Am0k-GIT/Soldering_station/case/gx16-8.SLDPRT

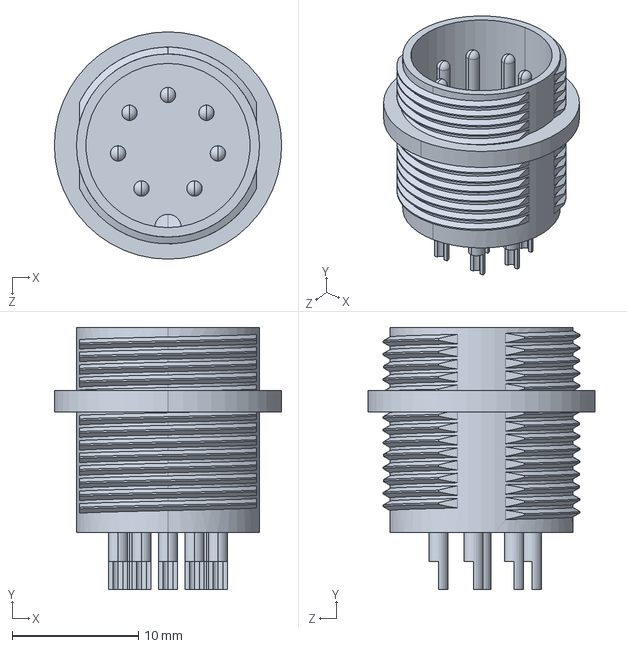
[picture p35: CAD file, 2025-12-07]
case/gx16-8.SLDPRT
18.0 x 20.8 x 18.0 mm
