Am0k-GIT/Soldering_station/case/shim_8_3.2_1.4.SLDPRT

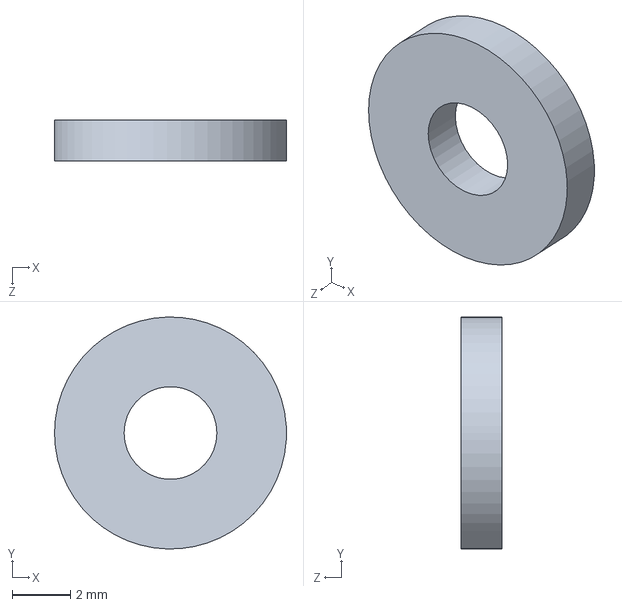
[picture p36: CAD file, 2025-12-07]
case/shim_8_3.2_1.4.SLDPRT
8.00 x 8.00 x 1.40 mm
