Am0k-GIT/Soldering_station/case/PC cooling fan.STEP

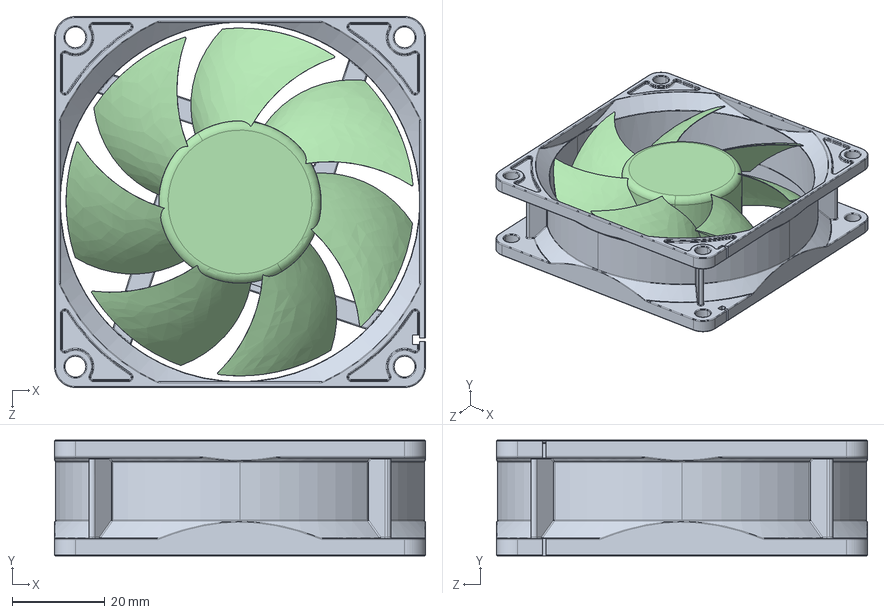
[picture p37: CAD file, 2025-12-07]
case/PC cooling fan.STEP
80.0 x 25.0 x 80.0 mm
fan body case
Part3^Assem1
fanl blade
