Am0k-GIT/Soldering_station/case/GX12-5 Jack.step

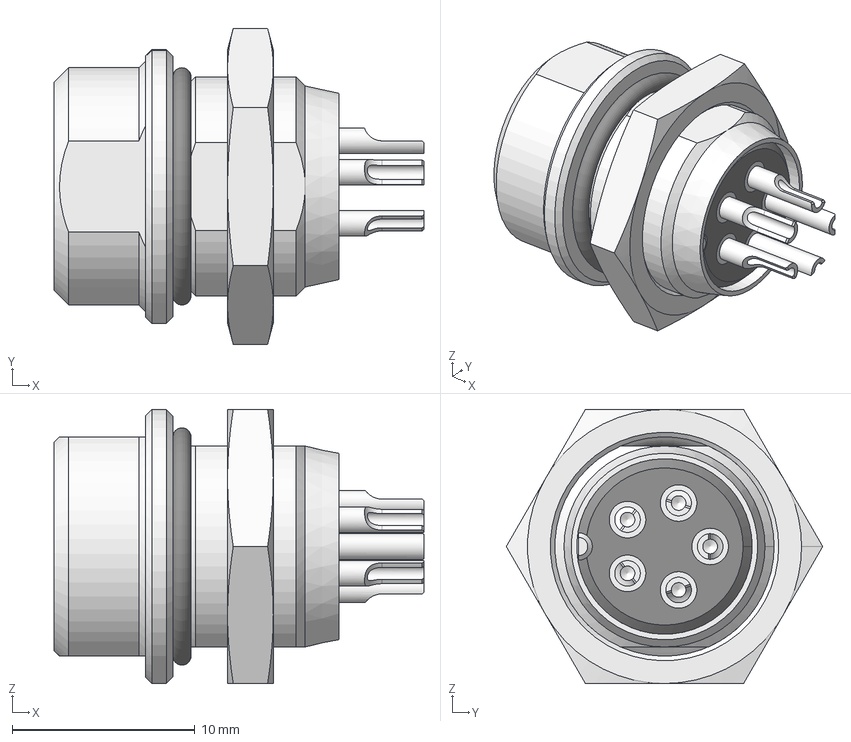
[picture p38: CAD file, 2025-12-07]
case/GX12-5 Jack.step
20.2 x 17.3 x 15.0 mm
