Am0k-GIT/Soldering_station/case/part_2.SLDPRT

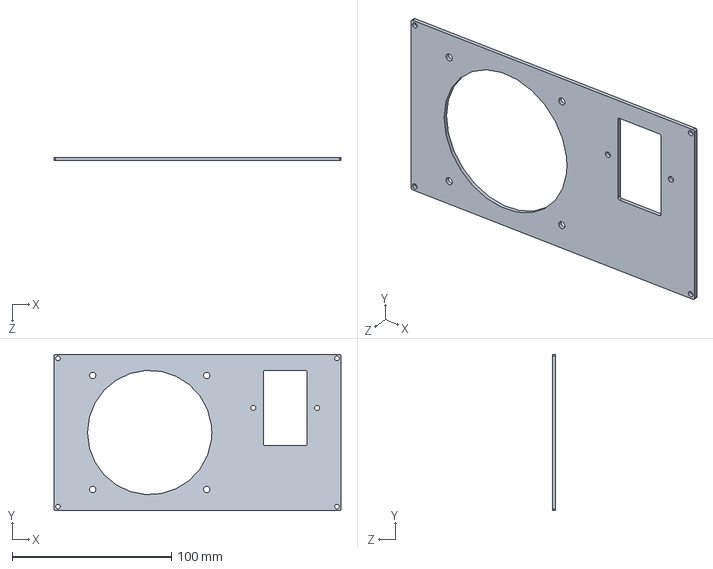
[picture p39: CAD file, 2025-12-07]
case/part_2.SLDPRT
180.0 x 98.0 x 2.00 mm
