Am0k-GIT/Soldering_station/case/frame.SLDPRT

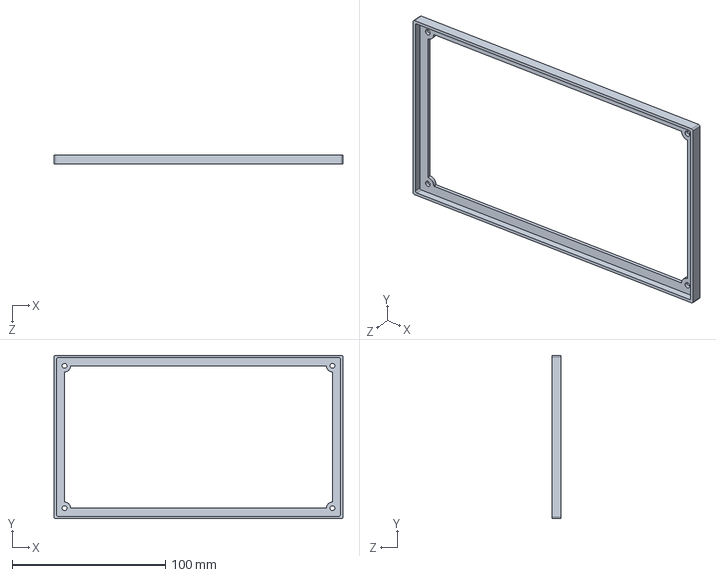
[picture p40: CAD file, 2025-12-07]
case/frame.SLDPRT
188.8 x 106.8 x 6.00 mm
