Am0k-GIT/Soldering_station/case/power_supply_mount.SLDPRT

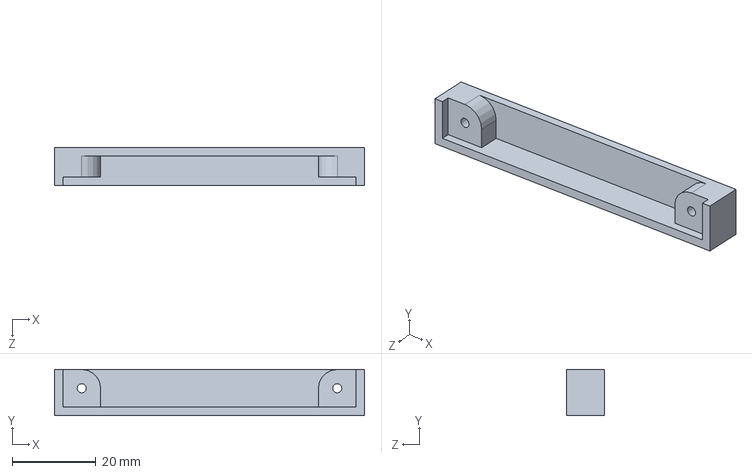
[picture p41: CAD file, 2025-12-07]
case/power_supply_mount.SLDPRT
74.0 x 11.0 x 9.00 mm
