Am0k-GIT/Soldering_station/software/Soldering_Station_260412/Core/Inc/24CXX/ee24.c

/************************************************************************************************************
**************    Include Headers
************************************************************************************************************/
#include "usart.h"

#include "ee24.h"
#if EE24_RTOS == EE24_RTOS_DISABLE
#elif EE24_RTOS == EE24_RTOS_CMSIS_V1
#include "cmsis_os.h"
#include "freertos.h"
#elif EE24_RTOS == EE24_RTOS_CMSIS_V2
#include "cmsis_os2.h"
#include "freertos.h"
#elif EE24_RTOS == EE24_RTOS_THREADX
#include "app_threadx.h"
#endif

/************************************************************************************************************
**************    Private Definitions
************************************************************************************************************/

#if (EE24_SIZE <= 2)
#define EE24_PSIZE     8
#elif (EE24_SIZE <= 16)
#define EE24_PSIZE     16
#else
#define EE24_PSIZE     32
#endif

/************************************************************************************************************
**************    Private Functions
************************************************************************************************************/

void EE24_Delay(uint32_t Delay);
void EE24_Lock(EE24_HandleTypeDef *Handle);
void EE24_UnLock(EE24_HandleTypeDef *Handle);

/***********************************************************************************************************/

void EE24_Delay(uint32_t Delay)
{
#if EE24_RTOS == EE24_RTOS_DISABLE
  HAL_Delay(Delay);
#elif (EE24_RTOS == EE24_RTOS_CMSIS_V1) || (EE24_RTOS == EE24_RTOS_CMSIS_V2)
  uint32_t d = (configTICK_RATE_HZ * Delay) / 1000;
  if (d == 0)
      d = 1;
  osDelay(d);
#elif EE24_RTOS == EE24_RTOS_THREADX
  uint32_t d = (TX_TIMER_TICKS_PER_SECOND * Delay) / 1000;
  if (d == 0)
    d = 1;
  tx_thread_sleep(d);
#endif
}

/***********************************************************************************************************/

void EE24_Lock(EE24_HandleTypeDef *Handle)
{
  while (Handle->Lock)
  {
    EE24_Delay(1);
  }
  Handle->Lock = 1;
}

/***********************************************************************************************************/

void EE24_UnLock(EE24_HandleTypeDef *Handle)
{
  Handle->Lock = 0;
}

/************************************************************************************************************
**************    Public Functions
************************************************************************************************************/

#if EE24_USE_WP_PIN == false
/**
  * @brief  Initialize EEPROM handle
  * @note   Initialize EEPROM handle and set EEPROM address
  *
  * @param  *Handle: Pointer to EE24_HandleTypeDef structure
  * @param  *HI2c: Pointer to I2C_HandleTypeDef structure
  * @param  I2CAddress: I2C Memory address
  *
  * @retval bool: true or false
  */
bool EE24_Init(EE24_HandleTypeDef *Handle, I2C_HandleTypeDef *HI2c, uint8_t I2CAddress)
{
  bool answer = false;
  do
  {
    if ((Handle == NULL) || (HI2c == NULL))
    {
      break;
    }
    Handle->HI2c = HI2c;
    Handle->Address = I2CAddress;
    if (HAL_I2C_IsDeviceReady(Handle->HI2c, Handle->Address, 2, 100) == HAL_OK)
    {
      answer = true;
    }
  }
  while (0);

  return answer;
}
#else
/**
  * @brief  Initialize EEPROM handle
  * @note   Initialize EEPROM handle and set memory address
  *
  * @param  *Handle: Pointer to EE24_HandleTypeDef structure
  * @param  *HI2c: Pointer to I2C_HandleTypeDef structure
  * @param  I2CAddress: I2C Memory address
  * @param  *GPIO_TypeDef: Pointer to GPIO_TypeDef structure for Write protected pin
  * @param  WpPin: PinNumber of write protected pin
  *
  * @retval bool: true or false
  */
bool EE24_Init(EE24_HandleTypeDef *Handle, I2C_HandleTypeDef *HI2c, uint8_t I2CAddress, GPIO_TypeDef *WpGpio, uint16_t WpPin)
{
  bool answer = false;
  do
  {
    if ((Handle == NULL) || (HI2c == NULL) || (WpGpio == NULL))
    {
      break;
    }
    Handle->HI2c = HI2c;
    Handle->Address = I2CAddress;
    Handle->WpGpio = WpGpio;
    Handle->WpPin = WpPin;
    HAL_GPIO_WritePin(Handle->WpGpio, Handle->WpPin, GPIO_PIN_SET);
    if (HAL_I2C_IsDeviceReady(Handle->HI2c, Handle->Address, 2, 100) == HAL_OK)
    {
      answer = true;
    }
  }
  while (0);

  return answer;
}
#endif

/***********************************************************************************************************/

/**
  * @brief  Read from Memory
  * @note   Read data from memory and copy to an array
  *
  * @param  *Handle: Pointer to EE24_HandleTypeDef structure
  * @param  Address: Start address for read
  * @param  *Data: Pointer to copy data from EEPROM
  * @param  Len: Data length to read
  * @param  Timeout: Timeout of this operation in ms
  *
  * @retval bool: true or false
  */
bool EE24_Read(EE24_HandleTypeDef *Handle, uint32_t Address, uint8_t *Data, size_t Len, uint32_t Timeout)
{
  EE24_Lock(Handle);
  bool answer = false;
  do
  {
#if ((EE24_SIZE == EE24_1KBIT) || (EE24_SIZE == EE24_2KBIT))
    if (HAL_I2C_Mem_Read(Handle->HI2c, Handle->Address, Address, I2C_MEMADD_SIZE_8BIT, Data, Len, Timeout) == HAL_OK)
#elif (EE24_SIZE == EE24_4KBIT)
    if (HAL_I2C_Mem_Read(Handle->HI2c, Handle->Address | ((Address & 0x0100) >> 7), (Address & 0xff), I2C_MEMADD_SIZE_8BIT, Data, Len, Timeout) == HAL_OK)
#elif (EE24_SIZE == EE24_8KBIT)
    if (HAL_I2C_Mem_Read(Handle->HI2c, Handle->Address | ((Address & 0x0300) >> 7), (Address & 0xff), I2C_MEMADD_SIZE_8BIT, Data, Len, Timeout) == HAL_OK)
#elif (EE24_SIZE == EE24_16KBIT)
    if (HAL_I2C_Mem_Read(Handle->HI2c, Handle->Address | ((Address & 0x0700) >> 7), (Address & 0xff), I2C_MEMADD_SIZE_8BIT, Data, Len, Timeout) == HAL_OK)
#else
    if (HAL_I2C_Mem_Read(Handle->HI2c, Handle->Address, Address, I2C_MEMADD_SIZE_16BIT, Data, Len, Timeout) == HAL_OK)
#endif
    {
      answer = true;
    }
  }
  while (0);

  EE24_UnLock(Handle);
  return answer;
}

/***********************************************************************************************************/

/**
  * @brief  Write to Memory
  * @note   Write an array to memory
  *
  * @param  *Handle: Pointer to EE24_HandleTypeDef structure
  * @param  Address: Start address for write
  * @param  *Data: Pointer to copy data to EEPEOM
  * @param  Len: Data length to write
  * @param  Timeout: Timeout of this operation in ms
  *
  * @retval bool: true or false
  */
bool EE24_Write(EE24_HandleTypeDef *Handle, uint32_t Address, uint8_t *Data, size_t Len, uint32_t Timeout)
{
  EE24_Lock(Handle);
  bool answer = false;
  do
  {
    uint16_t w;
    uint32_t startTime = HAL_GetTick();
#if EE24_USE_WP_PIN == true
    HAL_GPIO_WritePin(Handle->WpGpio, Handle->WpPin, GPIO_PIN_RESET);
#endif
    while (1)
    {
      w = EE24_PSIZE - (Address  % EE24_PSIZE);
      if (w > Len)
      {
        w = Len;
      }
#if ((EE24_SIZE == EE24_1KBIT) || (EE24_SIZE == EE24_2KBIT))
        if (HAL_I2C_Mem_Write(Handle->HI2c, Handle->Address, Address, I2C_MEMADD_SIZE_8BIT, Data, w, Timeout) == HAL_OK)
#elif (EE24_SIZE == EE24_4KBIT)
        if (HAL_I2C_Mem_Write(Handle->HI2c, Handle->Address | ((Address & 0x0100) >> 7), (Address & 0xff), I2C_MEMADD_SIZE_8BIT, Data, w, Timeout) == HAL_OK)
#elif (EE24_SIZE == EE24_8KBIT)
        if (HAL_I2C_Mem_Write(Handle->HI2c, Handle->Address | ((Address & 0x0300) >> 7), (Address & 0xff), I2C_MEMADD_SIZE_8BIT, Data, w, Timeout) == HAL_OK)
#elif (EE24_SIZE == EE24_16KBIT)
        if (HAL_I2C_Mem_Write(Handle->HI2c, Handle->Address | ((Address & 0x0700) >> 7), (Address & 0xff), I2C_MEMADD_SIZE_8BIT, Data, w, Timeout) == HAL_OK)
#else
        if (HAL_I2C_Mem_Write(Handle->HI2c, Handle->Address, Address, I2C_MEMADD_SIZE_16BIT, Data, w, Timeout) == HAL_OK)
#endif
      {
        EE24_Delay(10);
        Len -= w;
        Data += w;
        Address += w;
        if (Len == 0)
        {
          answer = true;
          break;
        }
        if (HAL_GetTick() - startTime >= Timeout)
        {
          break;
        }
      }
      else
      {
        break;
      }
    }
  }
  while (0);

#if EE24_USE_WP_PIN == true
    HAL_GPIO_WritePin(Handle->WpGpio, Handle->WpPin, GPIO_PIN_SET);
#endif
  EE24_UnLock(Handle);
  return answer;
}

/***********************************************************************************************************/

/**
  * @brief  Circle Write to Memory
  * @note   Write an array to memory
  *
  * @param  *Handle: Pointer to EE24_HandleTypeDef structure
  * @param  StartAddress: First Address for available memory block
  * @param  StopAddress: Last Address for available memory block
  * @param  FullCell: flag is cell not empty
  * @param  *Data: Pointer to copy data to EEPEOM
  * @param  Len: Data length to write
  * @param  Timeout: Timeout of this operation in ms
  *
  * @retval bool: true or false
  */
bool EE24_ReadCircle(EE24_HandleTypeDef *Handle, uint32_t StartAddress, uint32_t StopAddress, uint8_t FullCell, uint8_t *Data, size_t Len, uint32_t Timeout)
{
	if (StopAddress - StartAddress < Len)                                      // Check block size
		return 0;

    uint32_t counts = (StopAddress - StartAddress + 1)/(Len + 1);
    uint8_t buff;

    EE24_Read(Handle, StartAddress, &buff, 1u, 1000);
    if (buff == FullCell)
    {
      for (int32_t i = counts - 1; i >= 0; i--)
      {
    	uint32_t address = StartAddress + i * (Len + 1);

    	EE24_Read(Handle, address, &buff, 1u, 1000);

    	if (buff == FullCell)
    	{
            EE24_Read(Handle, address + 1, Data, Len, 1000);

        	return 1;
    	}
      }
    }

	return 0;
}

/***********************************************************************************************************/

/**
  * @brief  Circle Write to Memory
  * @note   Write an array to memory
  *
  * @param  *Handle: Pointer to EE24_HandleTypeDef structure
  * @param  Address: Start address for write
  * @param  *Data: Pointer to copy data to EEPEOM
  * @param  Len: Data length to write
  * @param  Timeout: Timeout of this operation in ms
  *
  * @retval bool: true or false
  */

bool EE24_WriteCircle(EE24_HandleTypeDef *Handle, uint32_t StartAddress, uint32_t StopAddress, uint8_t FullCell, uint8_t *Data, size_t Len, uint32_t Timeout)
{
    if (StopAddress - StartAddress < Len)                                      // Check block size
        return 0;

    uint32_t counts = (StopAddress - StartAddress + 1)/(Len + 1);

    uint8_t buff;
    uint8_t empty_byte = 0xFF;

    for (uint32_t i = 0; i < counts; i++)
    {
    	uint32_t address = StartAddress + i * (Len + 1);
    	EE24_Read(Handle, address, &buff, 1u, 1000);

    	if (buff != FullCell)
    	{
        	EE24_Write(Handle, address, &FullCell, 1u, 1000);
        	EE24_Write(Handle, address + 1, Data, Len, 1000);

        	return 1;
    	}
    }

    EE24_Write(Handle, StartAddress, &FullCell, 1u, 1000);
    EE24_Write(Handle, StartAddress + 1, Data, Len, 1000);

    for (uint32_t i = 1; i < counts; i++)
    {
    	uint32_t address = StartAddress + i * (Len + 1);
    	EE24_Write(Handle, address, &empty_byte, 1u, 1000);
    }

    return 1;
}
