Am0k-GIT/Soldering_station/software/Soldering_Station_260412/Core/Inc/st7735/images.h

#ifndef __ST7735_IMAGES_H__
#define __ST7735_IMAGES_H__

const uint16_t battery_10x16[16][10] = {
{0x0000,0x0000,0x0000,0xF81F,0xF81F,0xF81F,0xF81F,0x0000,0x0000,0x0000,},
{0x0000,0x0000,0x0000,0xF81F,0xF81F,0xF81F,0xF81F,0x0000,0x0000,0x0000,},
{0x0000,0x0000,0x0000,0xF81F,0xF81F,0xF81F,0xF81F,0x0000,0x0000,0x0000,},
{0x0000,0x0000,0xF81F,0x0000,0x0000,0x0000,0x0000,0xF81F,0x0000,0x0000,},
{0x0000,0x0000,0xF81F,0x0000,0x0000,0x0000,0x0000,0xF81F,0x0000,0x0000,},
{0x0000,0x0000,0xF81F,0x0000,0x0000,0x0000,0x0000,0xF81F,0x0000,0x0000,},
{0x0000,0x0000,0xF81F,0x0000,0x0000,0x0000,0x0000,0xF81F,0x0000,0x0000,},
{0x0000,0x0000,0xF81F,0x0000,0x0000,0x0000,0x0000,0xF81F,0x0000,0x0000,},
{0x0000,0x0000,0xF81F,0x0000,0x0000,0x0000,0x0000,0xF81F,0x0000,0x0000,},
{0x0000,0x0000,0xF81F,0x0000,0x0000,0x0000,0x0000,0xF81F,0x0000,0x0000,},
{0x0000,0x0000,0xF81F,0x0000,0x0000,0x0000,0x0000,0xF81F,0x0000,0x0000,},
{0x0000,0x0000,0xF81F,0x0000,0x0000,0x0000,0x0000,0xF81F,0x0000,0x0000,},
{0x0000,0x0000,0xF81F,0x0000,0x0000,0x0000,0x0000,0xF81F,0x0000,0x0000,},
{0x0000,0x0000,0xF81F,0x0000,0x0000,0x0000,0x0000,0xF81F,0x0000,0x0000,},
{0x0000,0x0000,0xF81F,0x0000,0x0000,0x0000,0x0000,0xF81F,0x0000,0x0000,},
{0x0000,0x0000,0xF81F,0xF81F,0xF81F,0xF81F,0xF81F,0xF81F,0x0000,0x0000,},
};

const uint16_t link_10x16[16][10] = {
{0x0000,0x0000,0x0000,0x001F,0x0000,0x0000,0x001F,0x0000,0x0000,0x0000,},
{0x0000,0x0000,0x001F,0x001F,0x001F,0x0000,0x001F,0x0000,0x0000,0x0000,},
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
{0x0000, 0x0000, 0x0000, 0x0000, 0x0000, 0x0000, 0x0000, 0x0000, 0x001F, 0x001F, 0x001F, 0x001F, 0x0000, 0x0000, 0x0000, 0x0000, 0x0000, 0x0000, 0x0000, 0x0000,},
};

#endif
