Am0k-GIT/Soldering_station/software/Soldering_Station_260412/Core/Inc/24CXX/ee24.h

#ifndef _EE24_H_
#define _EE24_H_

/***********************************************************************************************************

  Author:     Nima Askari
  Github:     https://www.github.com/NimaLTD
  LinkedIn:   https://www.linkedin.com/in/nimaltd
  Youtube:    https://www.youtube.com/@nimaltd
  Instagram:  https://instagram.com/github.NimaLTD

  Version:    3.2.0

  History:
              3.2.0
              - Added ThreadX Configuration

              3.1.0
              - Added WP pin control
              - Fix 1Kb and 2Kb memory writing

              3.0.1
              - Fixed Address
                        
              3.0.0
              - Rewrite again
              - Support STM32CubeMx Packet installer

  Am0k (https://github.com/Am0k-GIT) modified this library to add functions for circular
  writing and reading of data.

***********************************************************************************************************/

#ifdef __cplusplus
extern "C"
{
#endif

/************************************************************************************************************
**************    Include Headers
************************************************************************************************************/

#include <stdbool.h>
#include "i2c.h"
#include "24CXX/NimaLTD.I-CUBE-EE24_conf.h"

/************************************************************************************************************
**************    Public Definitions
************************************************************************************************************/

#define EE24_ADDRESS_DEFAULT 0xA0

/************************************************************************************************************
**************    Public struct/enum
************************************************************************************************************/

typedef struct
{
  I2C_HandleTypeDef      *HI2c;
  uint8_t                Address;
  uint8_t                Lock;
#if EE24_USE_WP_PIN == true
  GPIO_TypeDef           *WpGpio;
  uint16_t                WpPin;
#endif

} EE24_HandleTypeDef;

/************************************************************************************************************
**************    Public Functions
************************************************************************************************************/

#if EE24_USE_WP_PIN == false
bool EE24_Init(EE24_HandleTypeDef *Handle, I2C_HandleTypeDef *HI2c, uint8_t I2CAddress);
#else
bool EE24_Init(EE24_HandleTypeDef *Handle, I2C_HandleTypeDef *HI2c, uint8_t I2CAddress, GPIO_TypeDef *WpGpio, uint16_t WpPin);
#endif
bool EE24_Read(EE24_HandleTypeDef *Handle, uint32_t Address, uint8_t *Data, size_t Len, uint32_t Timeout);
bool EE24_Write(EE24_HandleTypeDef *Handle, uint32_t Address, uint8_t *Data, size_t Len, uint32_t Timeout);
bool EE24_ReadCircle(EE24_HandleTypeDef *Handle, uint32_t StartAddress,uint32_t StopAddress, uint8_t FullCell, uint8_t *Data, size_t Len, uint32_t Timeout);
bool EE24_WriteCircle(EE24_HandleTypeDef *Handle, uint32_t StartAddress,uint32_t StopAddress, uint8_t FullCell, uint8_t *Data, size_t Len, uint32_t Timeout);

#ifdef __cplusplus
}
#endif
#endif
