Am0k-GIT/Soldering_station/software/Soldering_Station_260412/Core/Inc/ADCconverter/ADCtables.h

/***********************************************************************************************************

  Author:     Am0k
  Github:     https://github.com/Am0k-GIT

***********************************************************************************************************/

#ifndef INC_ADC_TABLES_H_
#define INC_ADC_TABLES_H_

calibration_entry_t EPCOS_B57551G_10K_B3492[] = {
    { 3992,  -50 },
    { 3911,  -40 },
    { 3784,  -30 },
    { 3598,  -20 },
    { 3342,  -10 },
    { 3019,    0 },
    { 2644,   10 },
    { 2246,   20 },
    { 1856,   30 },
    { 1499,   40 },
    { 1191,   50 },
    {  937,   60 },
    {  734,   70 },
    {  574,   80 },
    {  451,   90 },
    {  355,  100 },
    {  282,  110 },
    {  225,  120 },
    {  181,  130 },
    {  147,  140 },
    {  120,  150 },
};

calibration_entry_t EPCOS_B57540G_10K_B3625[] = {
    { 4008,  -50 },
    { 3934,  -40 },
    { 3815,  -30 },
    { 3634,  -20 },
    { 3381,  -10 },
    { 3053,    0 },
    { 2668,   10 },
    { 2254,   20 },
    { 1848,   30 },
    { 1477,   40 },
    { 1161,   50 },
    {  902,   60 },
    {  698,   70 },
    {  540,   80 },
    {  419,   90 },
    {  327,  100 },
    {  257,  110 },
    {  204,  120 },
    {  163,  130 },
    {  131,  140 },
    {  106,  150 },
};

calibration_entry_t COMMON_NTC_10K_B3435[] = {
    { 3959,  -30 },
    { 3915,  -25 },
    { 3862,  -20 },
    { 3797,  -15 },
    { 3718,  -10 },
    { 3626,   -5 },
    { 3520,    0 },
    { 3398,    5 },
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
    {  756,   85 },
    {  665,   90 },
    {  584,   95 },
    {  512,  100 },
    {  452,  105 },
    {  398,  110 }
};

calibration_entry_t thermocouple_type_K[] = {
    {   50,    0 },
    {  600,  120 },
    { 1330,  240 },
    { 2040,  360 }
};


#endif /* INC_ADC_TABLES_H_ */
